wirthda/usb-oscilloscope/docs/img/Architektur_SW_USB_Oszi.drawio.png

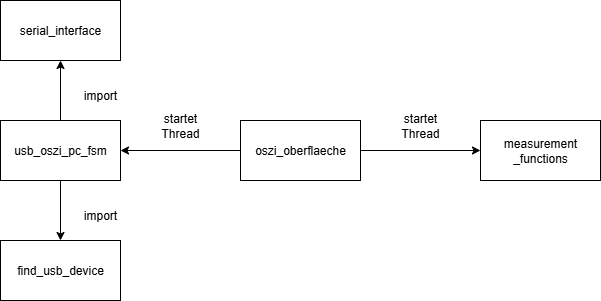
docs/img/Architektur_SW_USB_Oszi.drawio.png
