wirthda/usb-oscilloscope/docs/img/Baugruppe_Bild.jpg

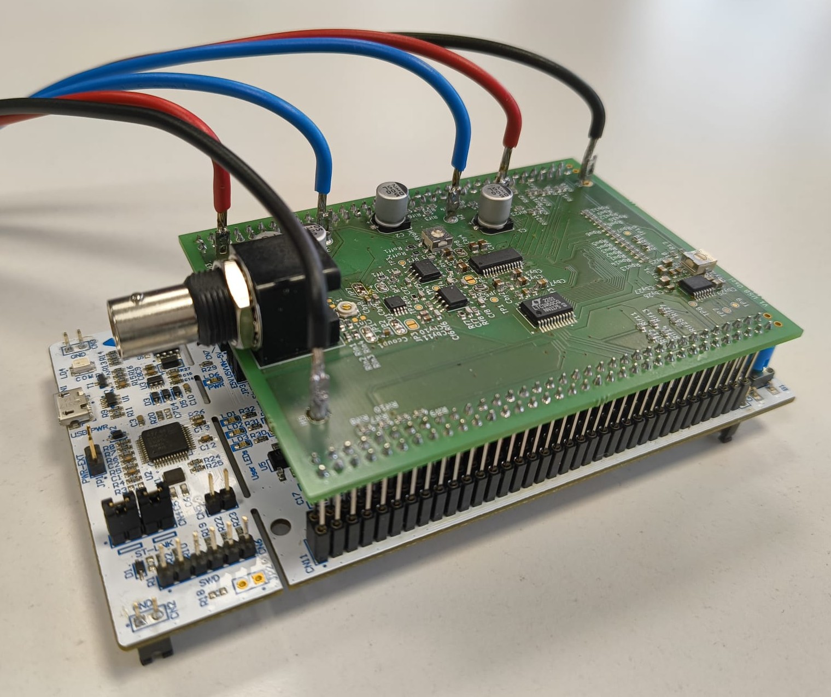
docs/img/Baugruppe_Bild.jpg
