wirthda/usb-oscilloscope/docs/img/StateDiagram_Firmware_V1_reduced.png

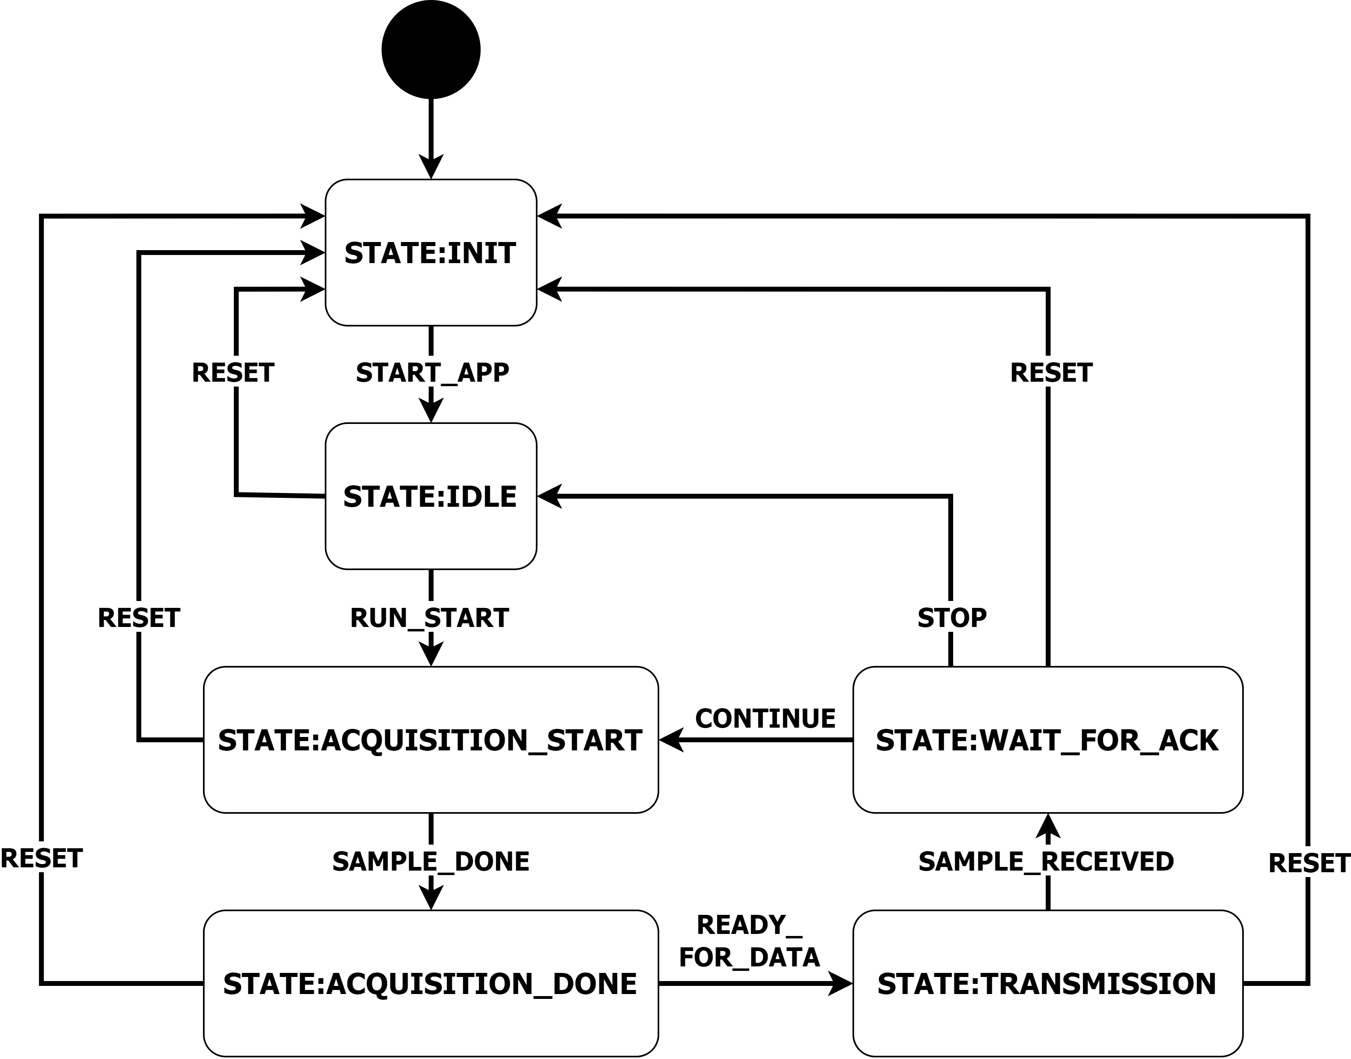
docs/img/StateDiagram_Firmware_V1_reduced.png
