wirthda/usb-oscilloscope/docs/img/statemaschine_GUI.png

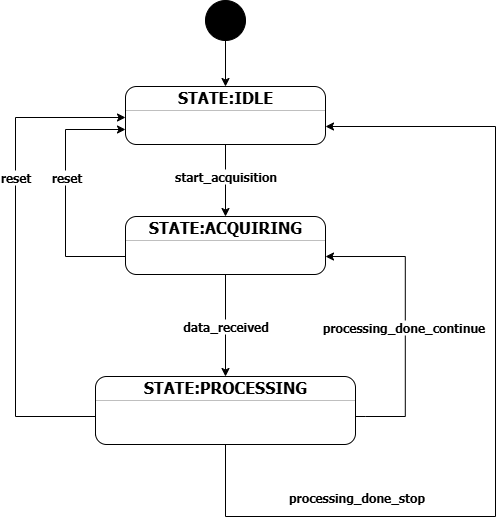
docs/img/statemaschine_GUI.png
