wirthda/usb-oscilloscope/sim/PSpice/AnalogesFrontend/Einzelkomponenten/AAF/AAF.png

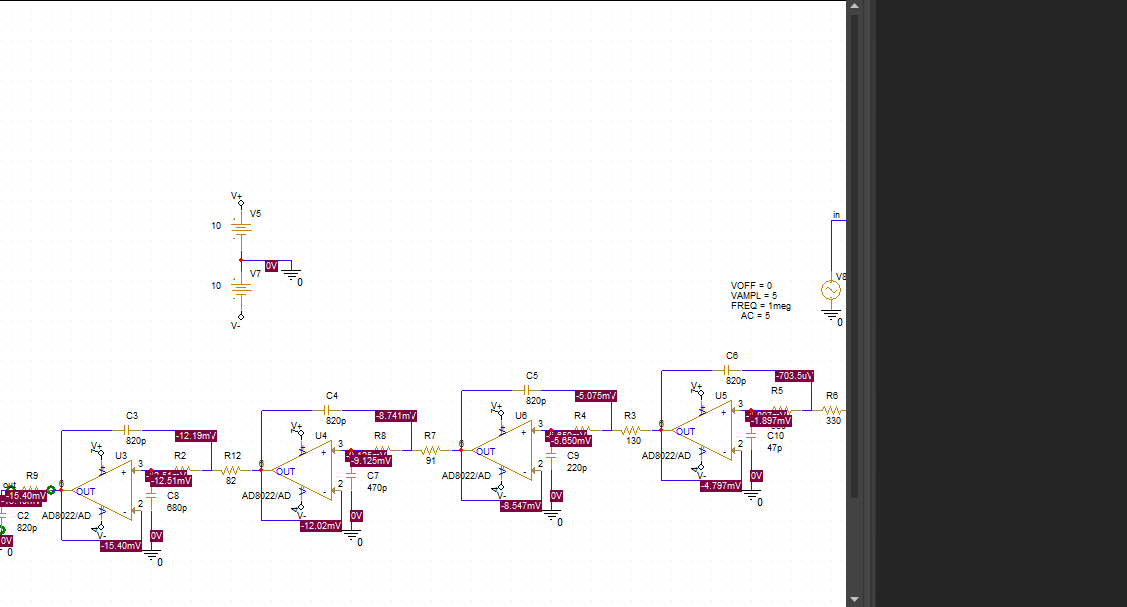
sim/PSpice/AnalogesFrontend/Einzelkomponenten/AAF/AAF.png
