wirthda/usb-oscilloscope/sim/PSpice/AnalogesFrontend/Gesamt/ANALOGES_FRONTEND_SIMULATION.png

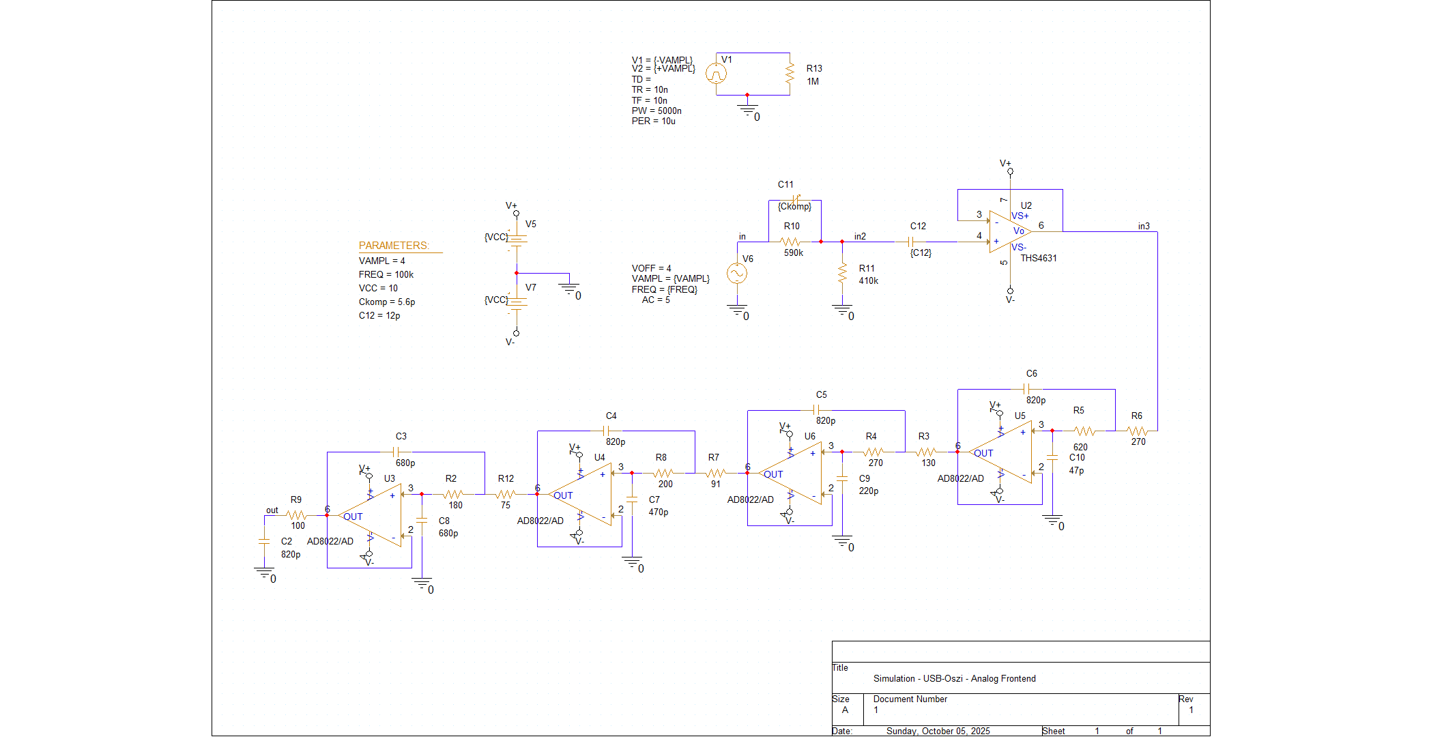
sim/PSpice/AnalogesFrontend/Gesamt/ANALOGES_FRONTEND_SIMULATION.png
