wirthda/usb-oscilloscope/docs/img/CubeIDE_Debug_View_Samples_raw.png

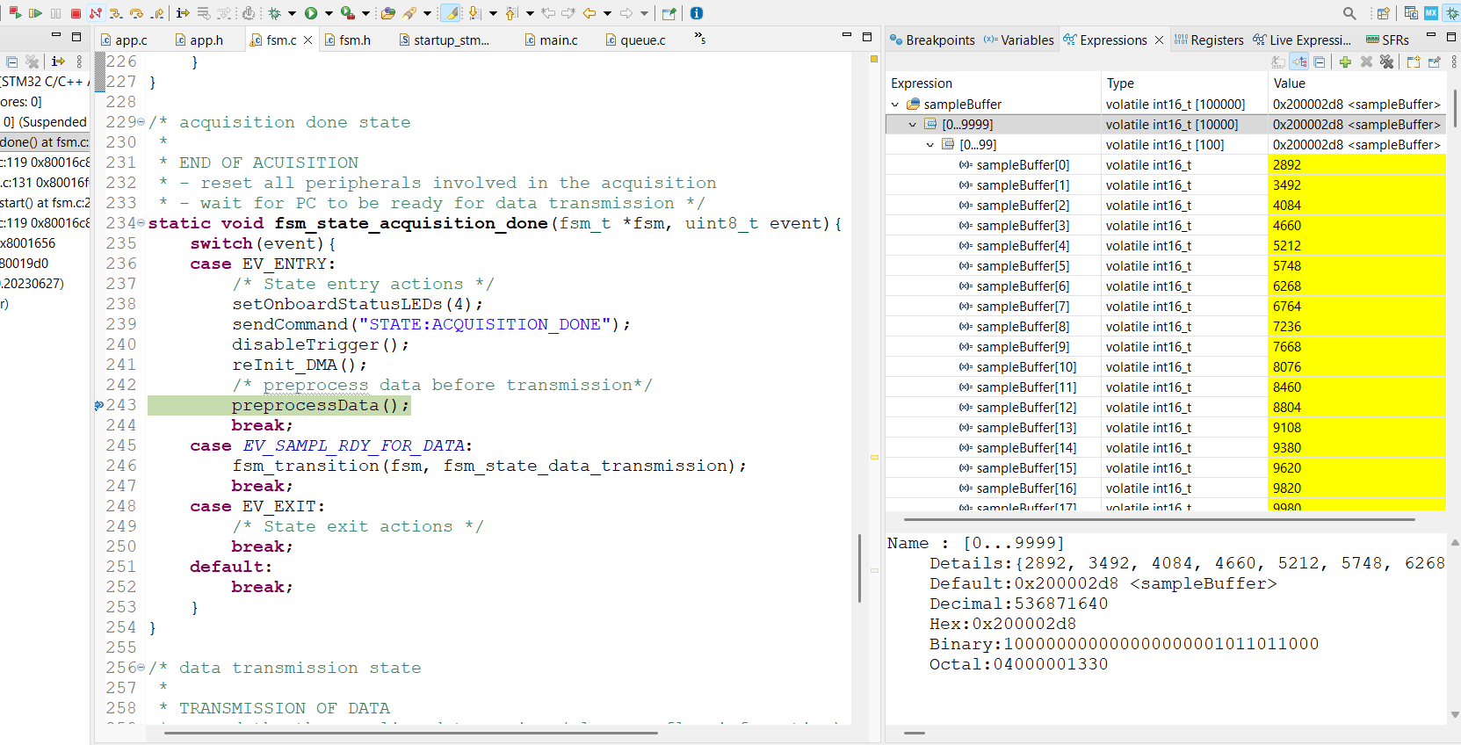
docs/img/CubeIDE_Debug_View_Samples_raw.png
