wirthda/usb-oscilloscope/cad/KiCad/USB_Oszi/Layout_Bottom.pdf

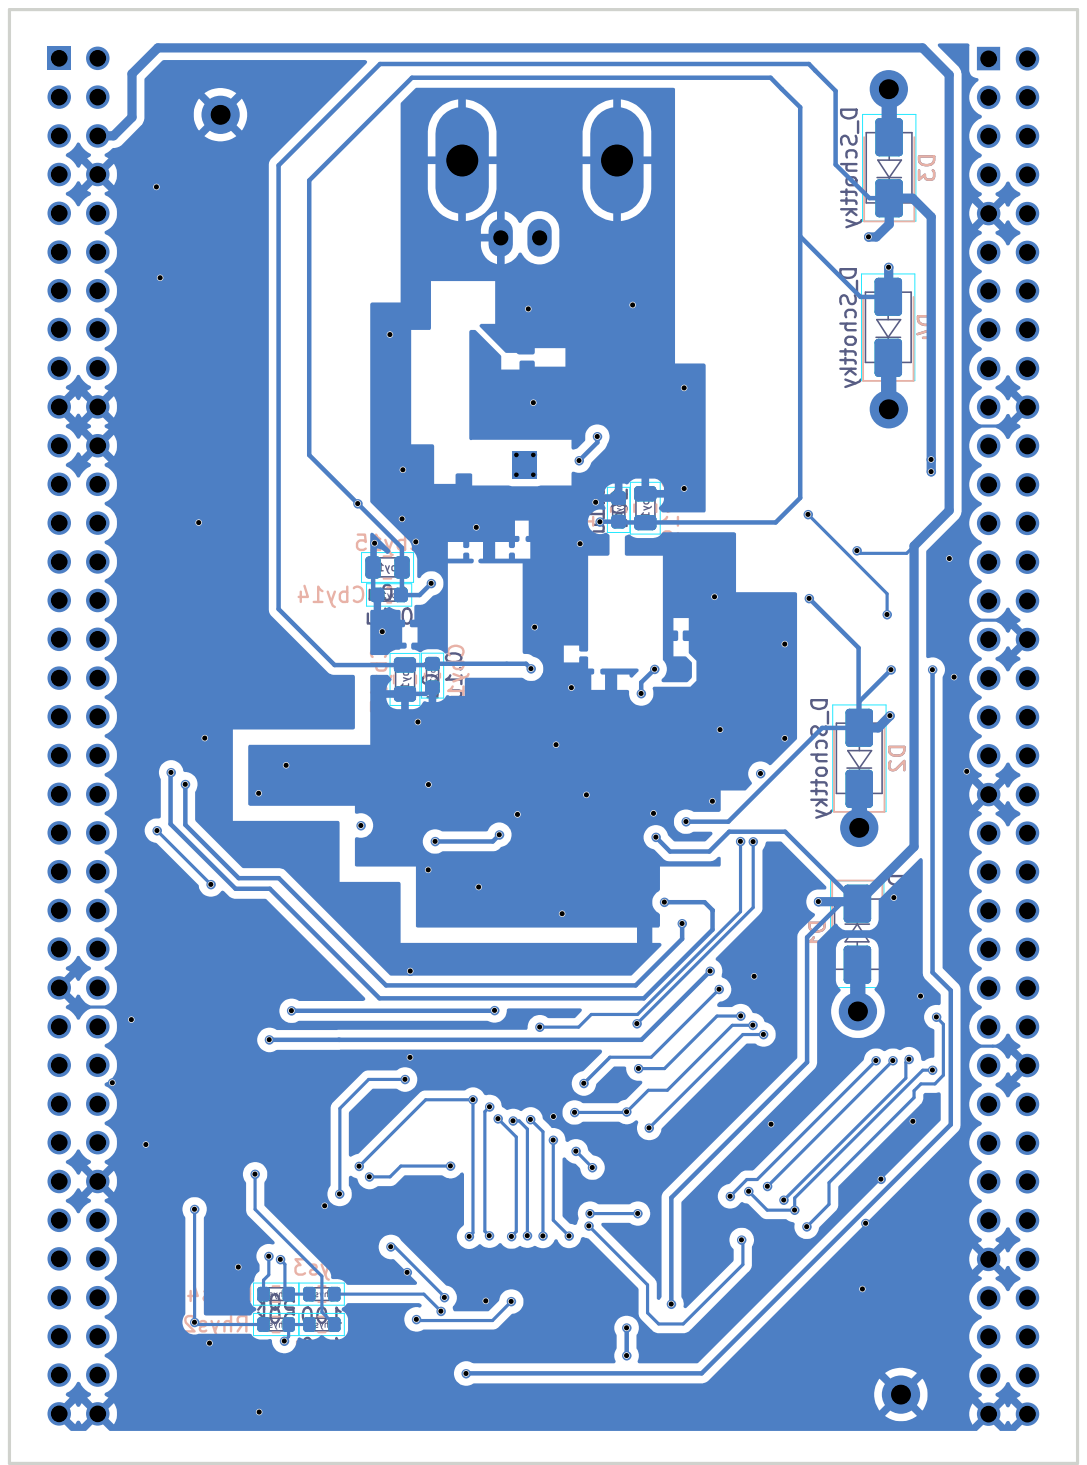
[picture p156: page 1]
