wirthda/usb-oscilloscope/cad/KiCad/USB_Oszi/Layout_Top.pdf

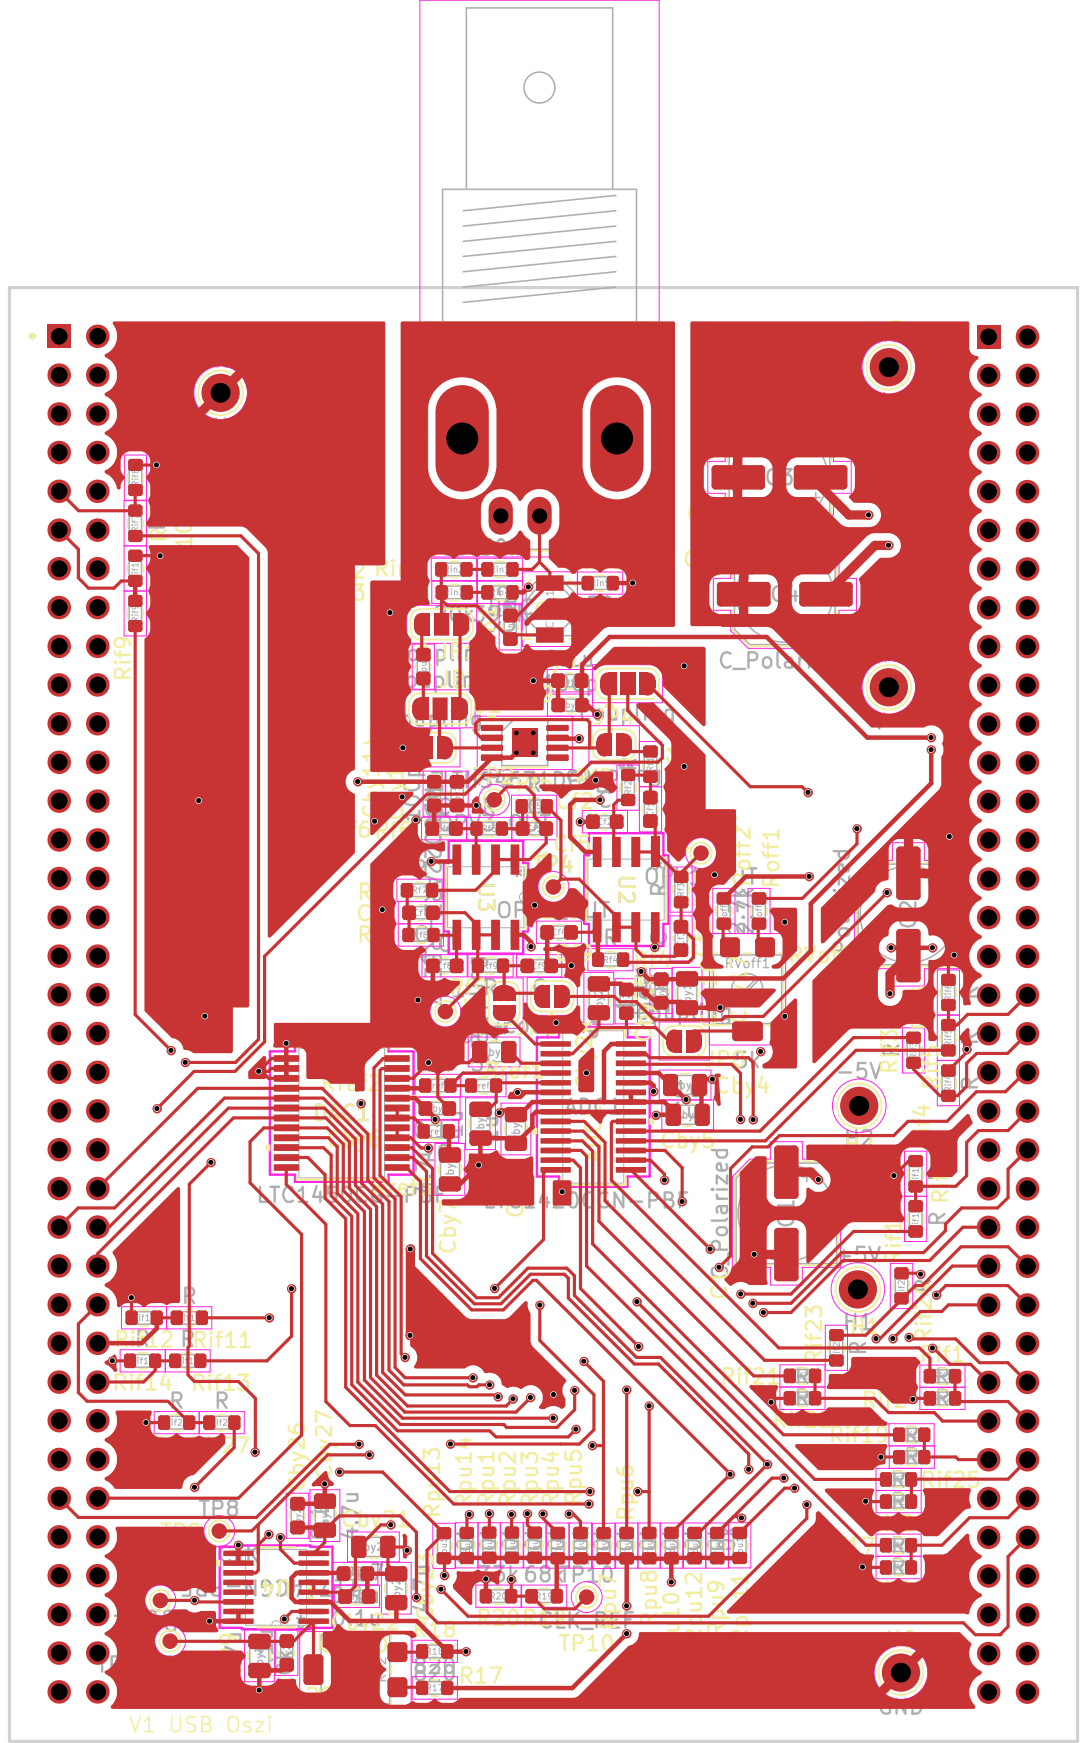
[picture p157: page 1]
