wirthda/usb-oscilloscope/sim/PSpice/AnalogesFrontend/Gesamt/Analoges_Frontend_Simulation-PSpiceFiles/SCHEMATIC1/bias/bias.cir

** Profile: "SCHEMATIC1-bias"  [ C:\dev\Projekt\PSpice\AnalogesFrontend\Gesamt\analoges_frontend_simulation-pspicefiles\schematic1\bias.sim ] 

** Creating circuit file "bias.cir" 
** WARNING: THIS AUTOMATICALLY GENERATED FILE MAY BE OVERWRITTEN BY SUBSEQUENT SIMULATIONS

*Libraries: 
* Profile Libraries :
* Local Libraries :
.LIB "C:/dev/Projekt/PSpice/LIB/ths4631_b.lib" 
* From [PSPICE NETLIST] section of C:\Users\samue\AppData\Roaming\SPB_Data\cdssetup\OrCAD_PSpice\25.1.0\PSpice.ini file:
.lib "nom.lib" 

*Analysis directives: 
.AC LIN 1000 10k 1G
.OPTIONS ADVCONV
.PROBE64 V(alias(*)) I(alias(*)) W(alias(*)) D(alias(*)) NOISE(alias(*)) 
.INC "..\SCHEMATIC1.net" 


.END
